AssilMAHFOUDI/Projet-2-Carte-de-developpement-ESP32/3d/430481025816/430481025816.stp

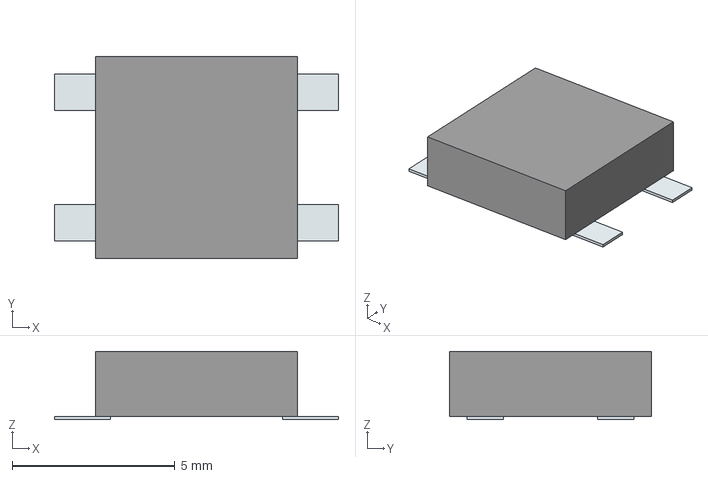
[picture p36: CAD file, 2024-11-25]
3d/430481025816/430481025816.stp
8.72 x 6.20 x 2.10 mm
Pins
