AssilMAHFOUDI/Projet-2-Carte-de-developpement-ESP32/3d/744232090/744232090.stp

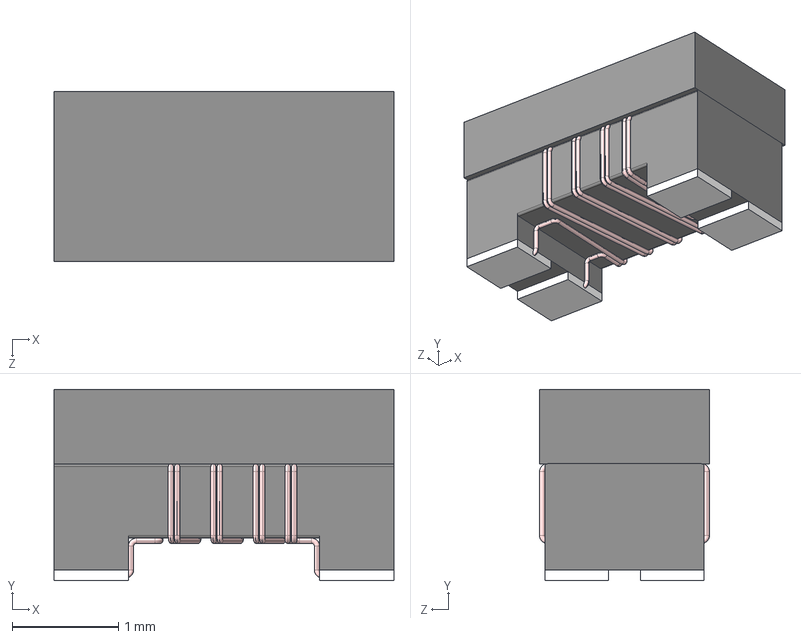
[picture p37: CAD file, 2024-11-25]
3d/744232090/744232090.stp
3.20 x 1.80 x 1.60 mm
